scottalmond/defcon_31/doc/ideas_space_bits/img/delete_me2.png

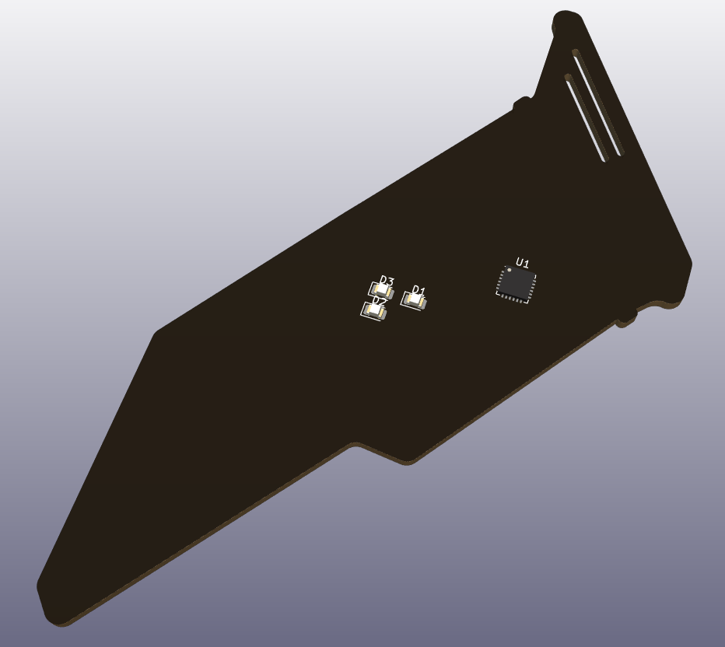
doc/ideas_space_bits/img/delete_me2.png
