scottalmond/defcon_31/doc/ideas_space_bits/img/draft_2f.png

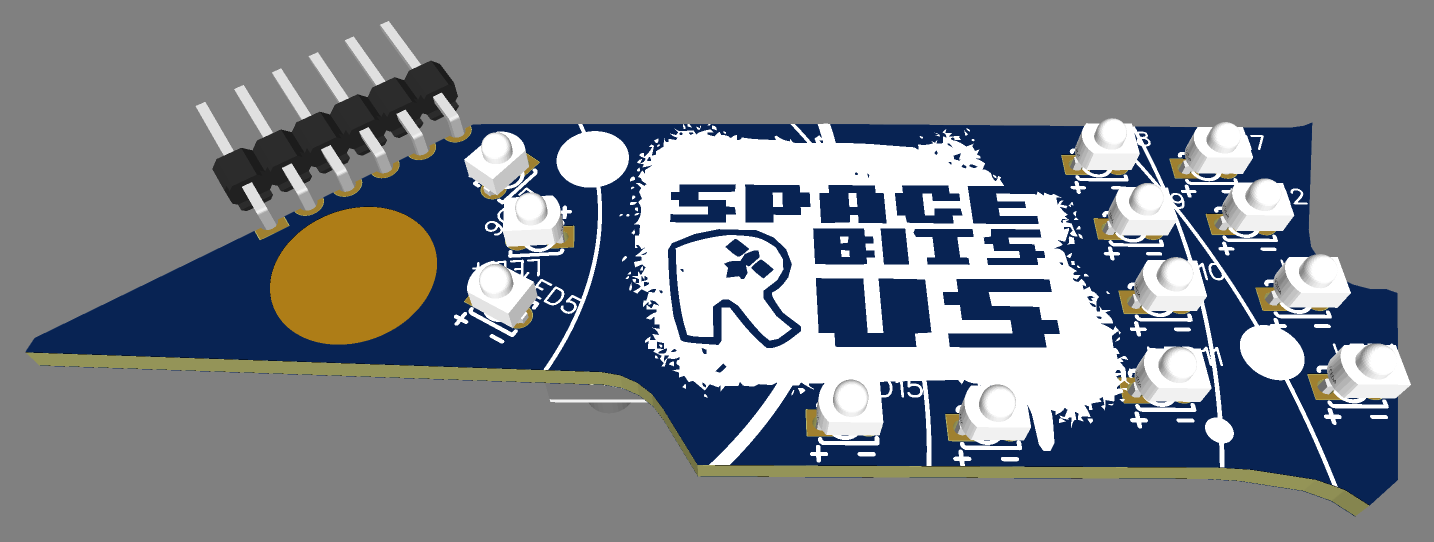
doc/ideas_space_bits/img/draft_2f.png
