scottalmond/defcon_31/doc/ideas_space_bits/img/draft_3r.png

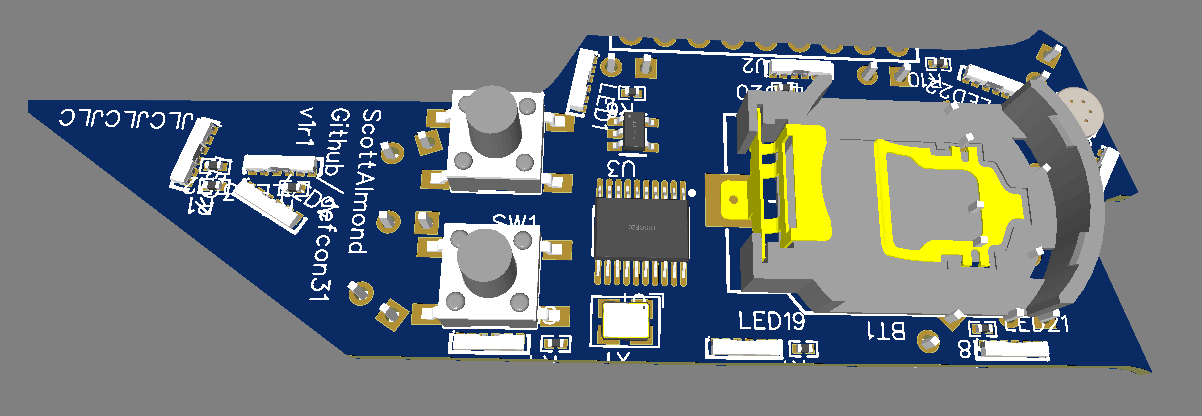
doc/ideas_space_bits/img/draft_3r.png
