scottalmond/defcon_31/doc/ideas_space_bits/img/draft_4f.png

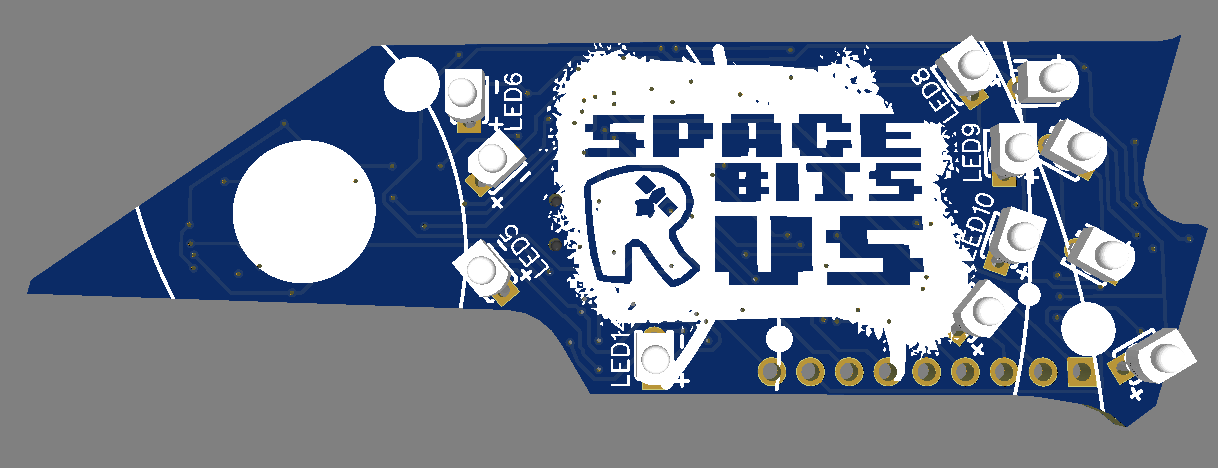
doc/ideas_space_bits/img/draft_4f.png
