scottalmond/defcon_31/doc/ideas_space_bits/img/LED_Final-2_696x464.webp

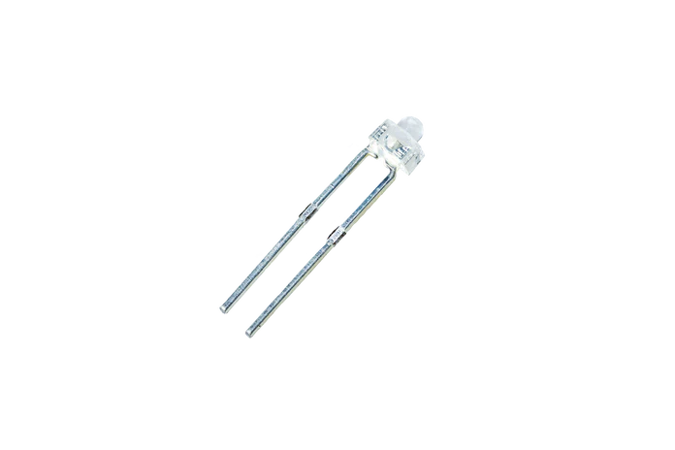
doc/ideas_space_bits/img/LED_Final-2_696x464.webp
