scottalmond/defcon_31/doc/ideas_space_bits/img/Produce_DanZhi.SMT_Snapshot.Bottom.3480359A_Y9.SMT02306191283897.png

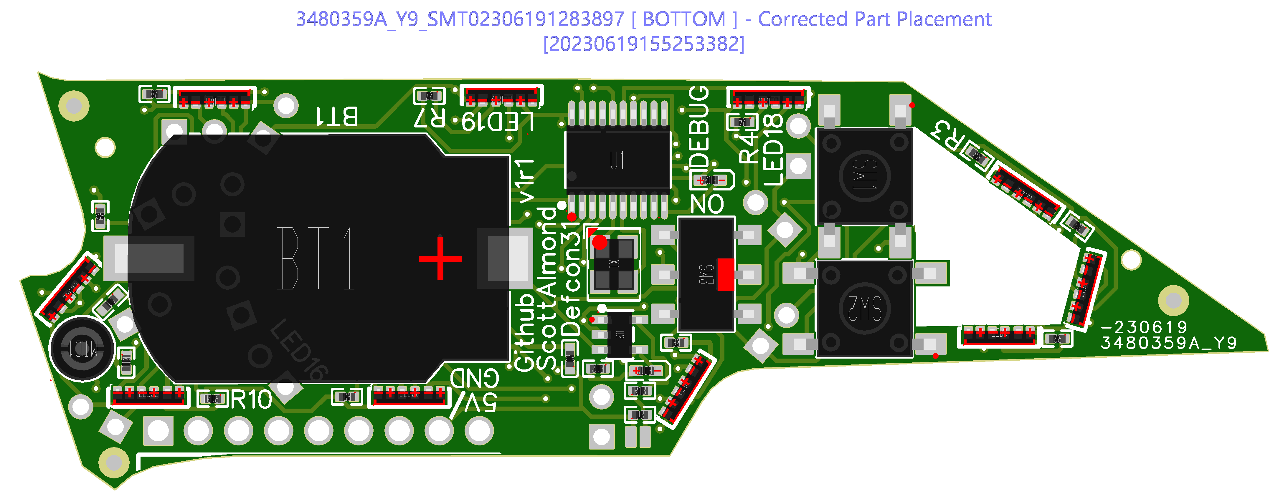
doc/ideas_space_bits/img/Produce_DanZhi.SMT_Snapshot.Bottom.3480359A_Y9.SMT02306191283897.png
