scottalmond/defcon_31/doc/ideas_space_bits/img/rainbow_acrylic4.png

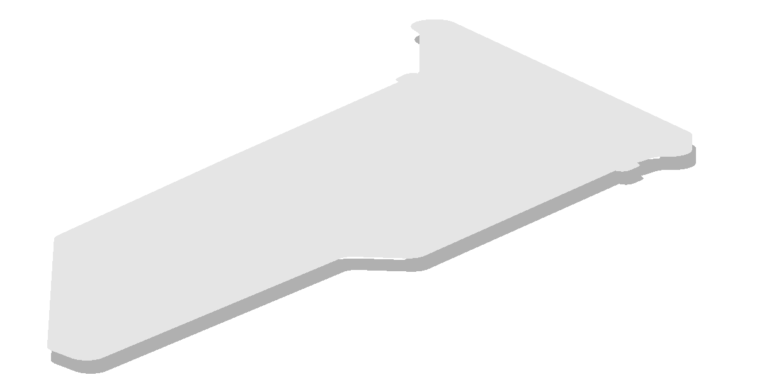
doc/ideas_space_bits/img/rainbow_acrylic4.png
