scottalmond/defcon_31/doc/ideas_space_bits/img/rainbow_acrylic5.png

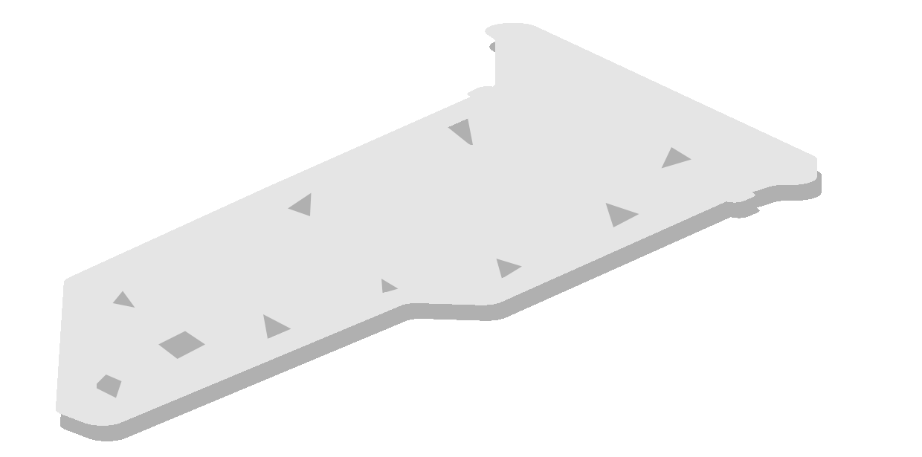
doc/ideas_space_bits/img/rainbow_acrylic5.png
