scottalmond/defcon_31/doc/ideas_space_bits/img/rainbow_acrylic7.png

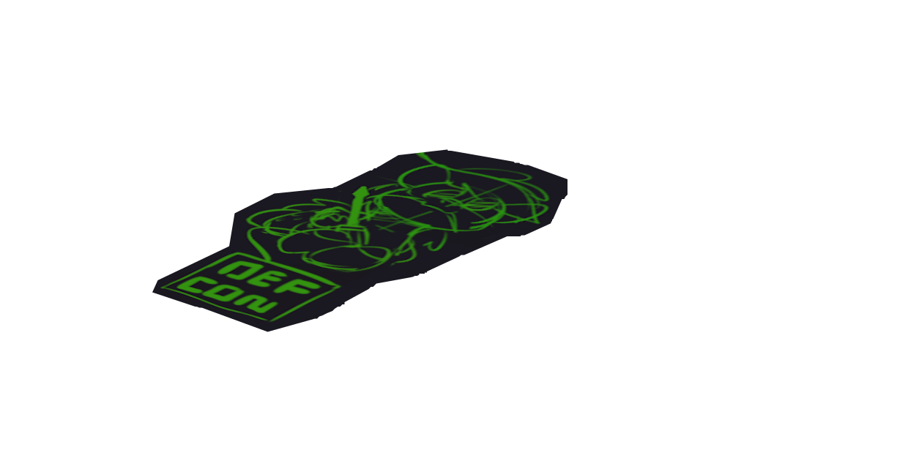
doc/ideas_space_bits/img/rainbow_acrylic7.png
