scottalmond/defcon_31/doc/ref/large_display_9ebfe82a-f162-4f1e-9fff-2418cbbd6314.jpg

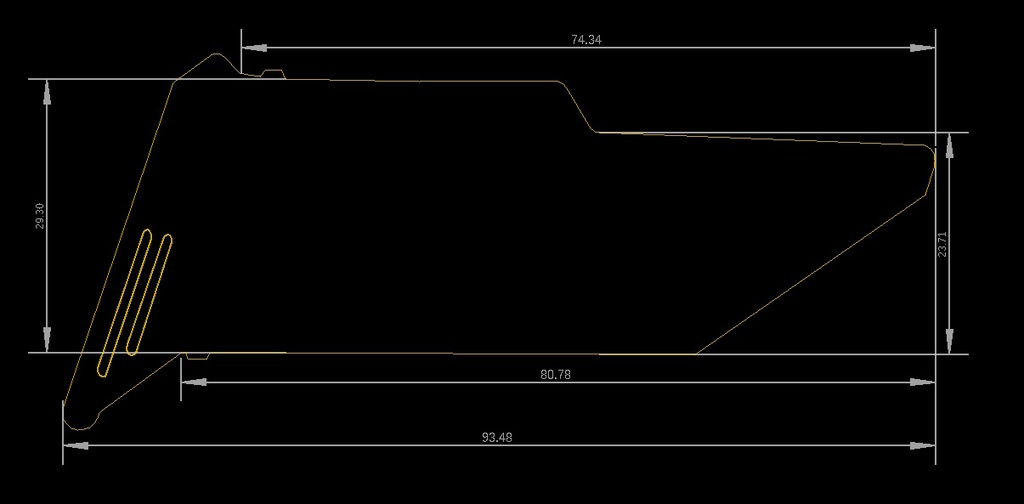
doc/ref/large_display_9ebfe82a-f162-4f1e-9fff-2418cbbd6314.jpg
