scottalmond/defcon_31/pcb/fab/v1r2/PCB_PCB_Space_Pony_Prototype_1_2023-07-18_bottom.png

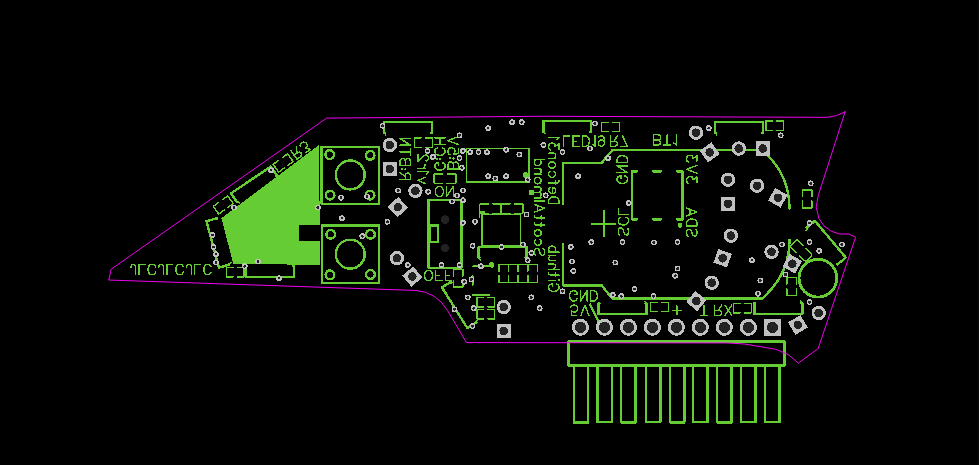
pcb/fab/v1r2/PCB_PCB_Space_Pony_Prototype_1_2023-07-18_bottom.png
