scottalmond/defcon_31/pcb/fab/v1r2/PCB_PCB_Space_Pony_Prototype_1_2023-07-18_v3.png

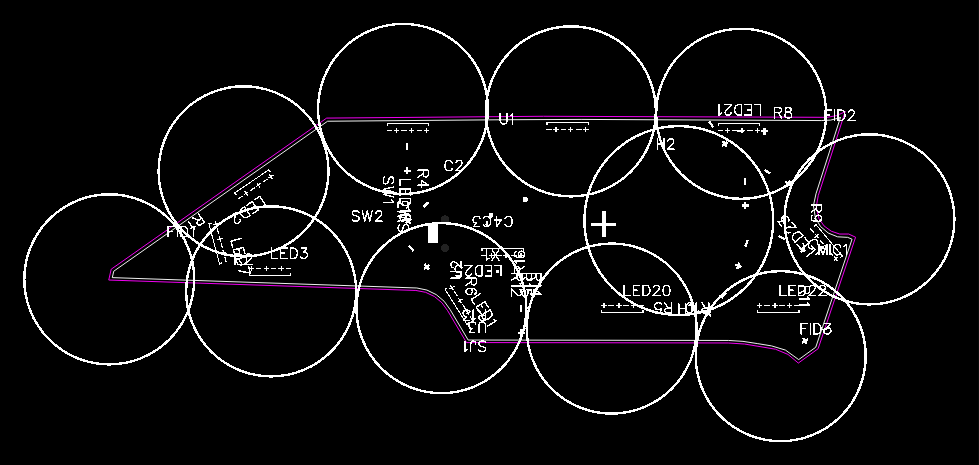
pcb/fab/v1r2/PCB_PCB_Space_Pony_Prototype_1_2023-07-18_v3.png
