scottalmond/defcon_31/doc/ref/files/DC31_SAO_Insert.stl

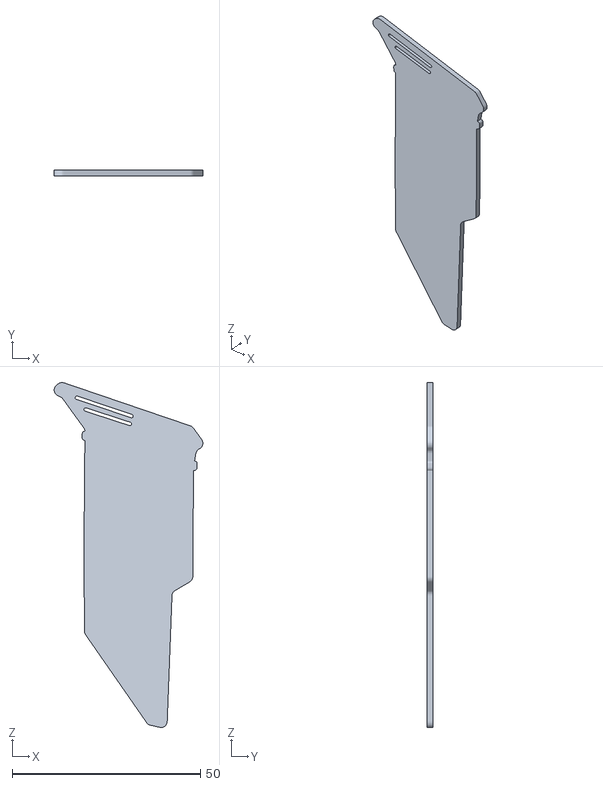
[picture p51: CAD file, 2023-06-09]
doc/ref/files/DC31_SAO_Insert.stl
39.5 x 1.60 x 91.5
