scottalmond/defcon_31/doc/ref/files/dc31_badge_bottom.stl

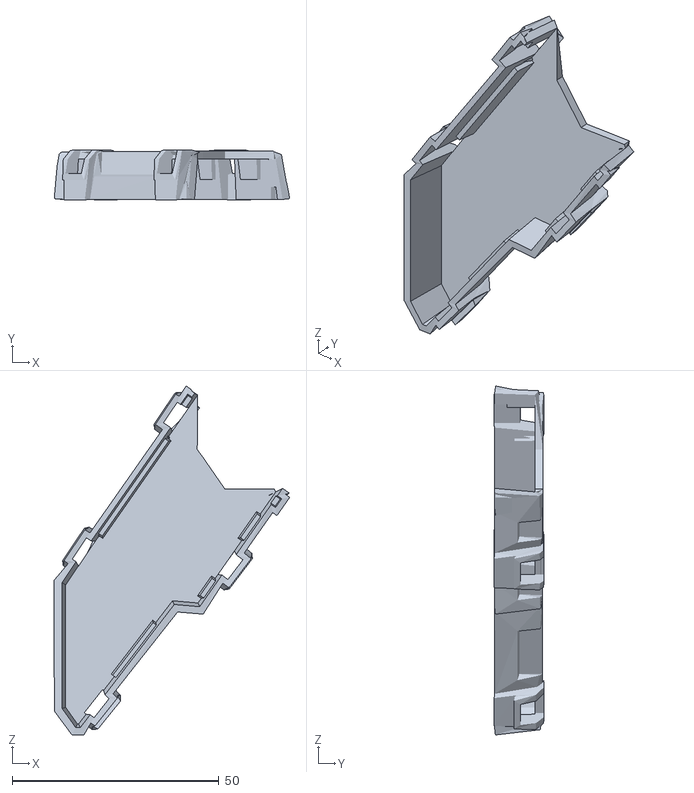
[picture p52: CAD file, 2023-06-09]
doc/ref/files/dc31_badge_bottom.stl
57.0 x 12.1 x 84.5
