scottalmond/defcon_31/cad/3d_print_lipo_502540_v1-BodyPad.stl

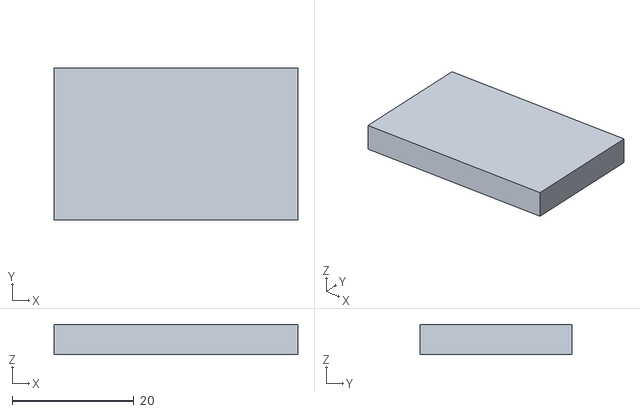
[picture p53: CAD file, 2023-06-12]
cad/3d_print_lipo_502540_v1-BodyPad.stl
40.0 x 25.0 x 5.00
