scottalmond/defcon_31/cad/3d_print_acrylic_pcb_outlines_v1.FCStd

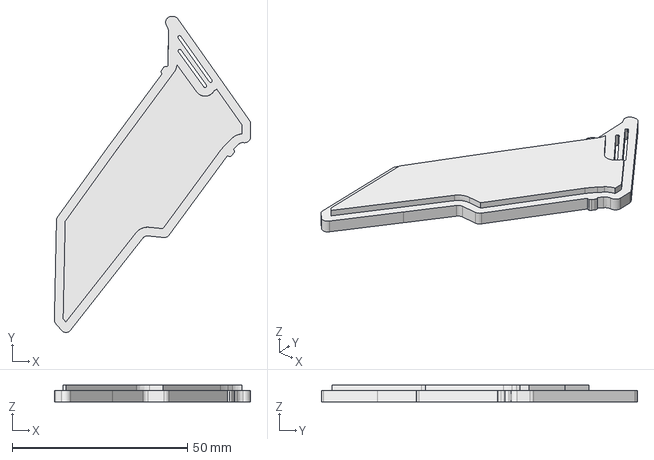
[picture p54: CAD file, 2023-06-12]
cad/3d_print_acrylic_pcb_outlines_v1.FCStd
56.1 x 90.2 x 4.78 mm
