scottalmond/defcon_31/cad/3d_print_lipo_402530_v1-BodyPad.stl

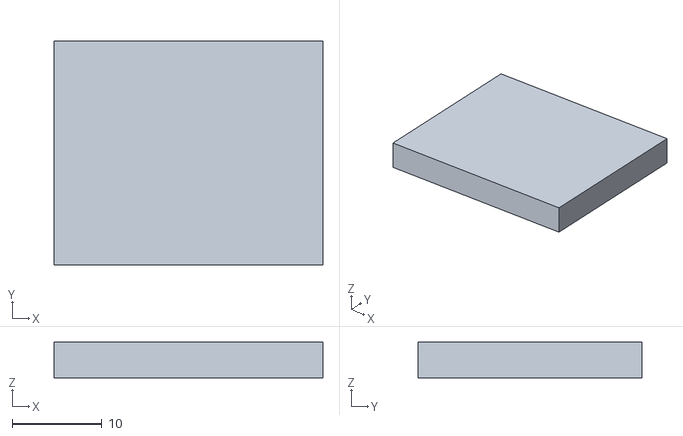
[picture p55: CAD file, 2023-06-12]
cad/3d_print_lipo_402530_v1-BodyPad.stl
30.0 x 25.0 x 4.00
