scottalmond/defcon_31/src/sduino/xiao_samd21_serialto/xiao_samd21_serialto.ino

// Code from https://wiki.seeedstudio.com/Seeeduino-XIAO-by-Nanase/
// This code will loopback the UART so that you can connect to another
// UART device
// Used this to talk to a STM8 Breakout Board on D5 and D6
// Note: Need to install version 1.8.1 in Board Manager
// Board = SeeedStudio XIAO
void setup() {
  Serial.begin(9600);
  Serial1.begin(9600);
}

void loop() {
  if (Serial.available()) {
    char c = (char)Serial.read();
    Serial1.write(c);
  }

  if (Serial1.available()) {
    char c = (char)Serial1.read();
    Serial.write(c);
  }
}
